fjmilens3/cody-computer/STL/CaseBadgeInlay.stl

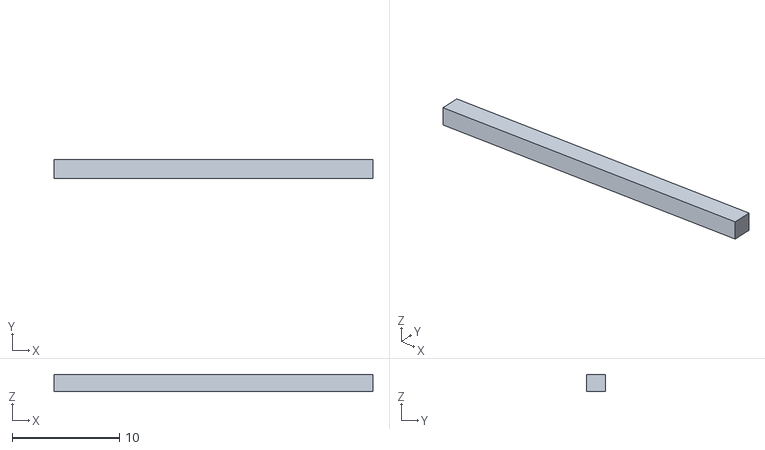
[picture p10: CAD file, 2024-12-14]
STL/CaseBadgeInlay.stl
29.8 x 1.80 x 1.60
