fjmilens3/cody-computer/STL/CartridgeBottom.stl

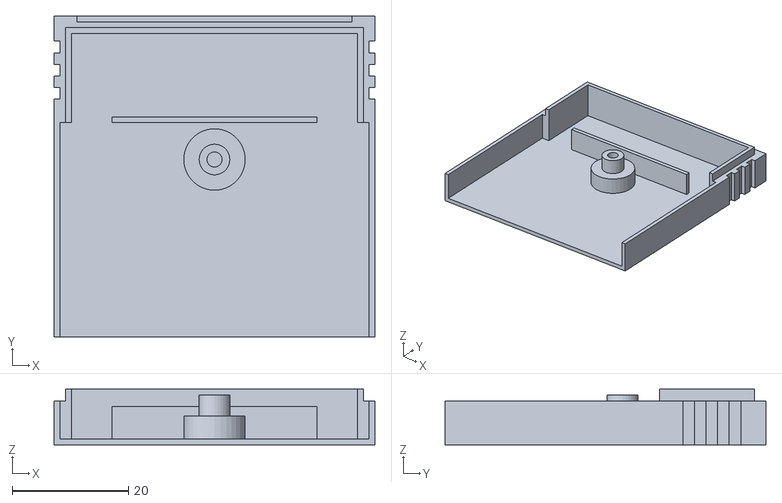
[picture p11: CAD file, 2024-12-14]
STL/CartridgeBottom.stl
55.3 x 55.3 x 9.60
