fjmilens3/cody-computer/STL/LEDHolder.stl

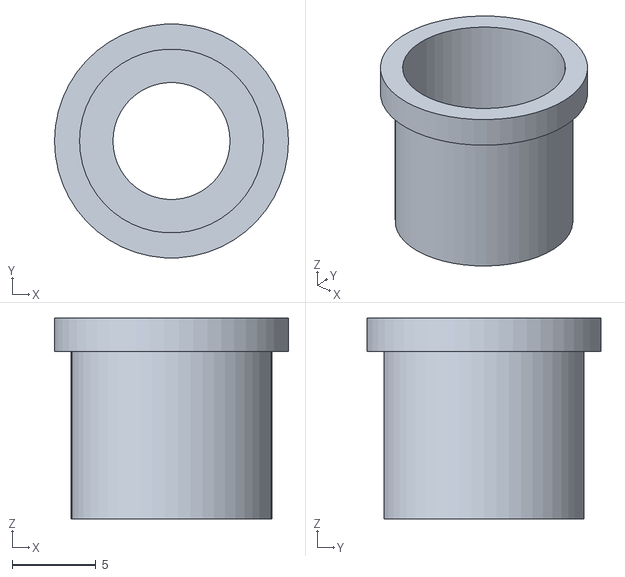
[picture p12: CAD file, 2024-12-14]
STL/LEDHolder.stl
14.0 x 14.0 x 12.0
