fjmilens3/cody-computer/STL/Keychain.stl

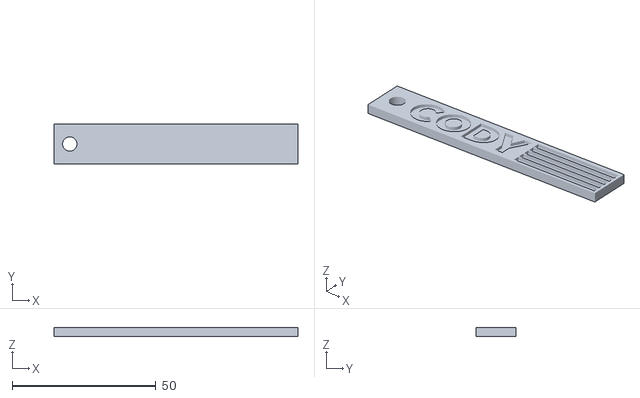
[picture p13: CAD file, 2024-12-14]
STL/Keychain.stl
85.0 x 14.0 x 3.00
