fjmilens3/cody-computer/STL/Spacebar.stl

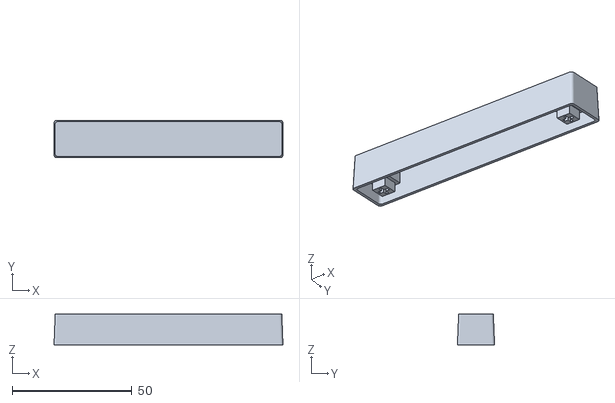
[picture p14: CAD file, 2024-12-14]
STL/Spacebar.stl
95.5 x 15.5 x 12.9
